arunderwood/milsblo/elec/src/parts/UNI_ROYAL_0603WAF1000T5E/R0603.STEP

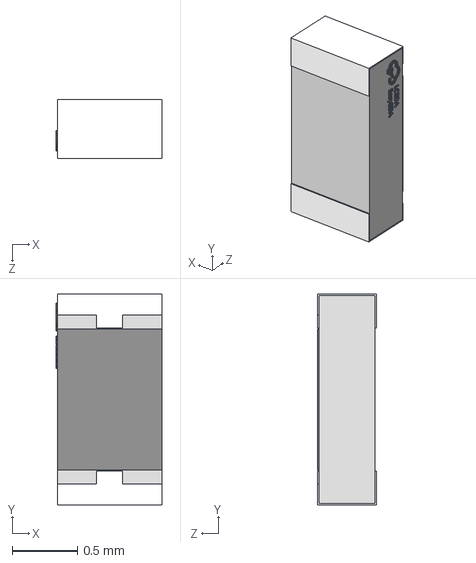
[picture p15: CAD file, 2026-02-18]
elec/src/parts/UNI_ROYAL_0603WAF1000T5E/R0603.STEP
0.81 x 1.62 x 0.45 mm
