arunderwood/milsblo/elec/src/parts/WCH_CH224K/ESSOP-10_L4.9-W3.9-P1.0-LS6.0-TL-EP.step

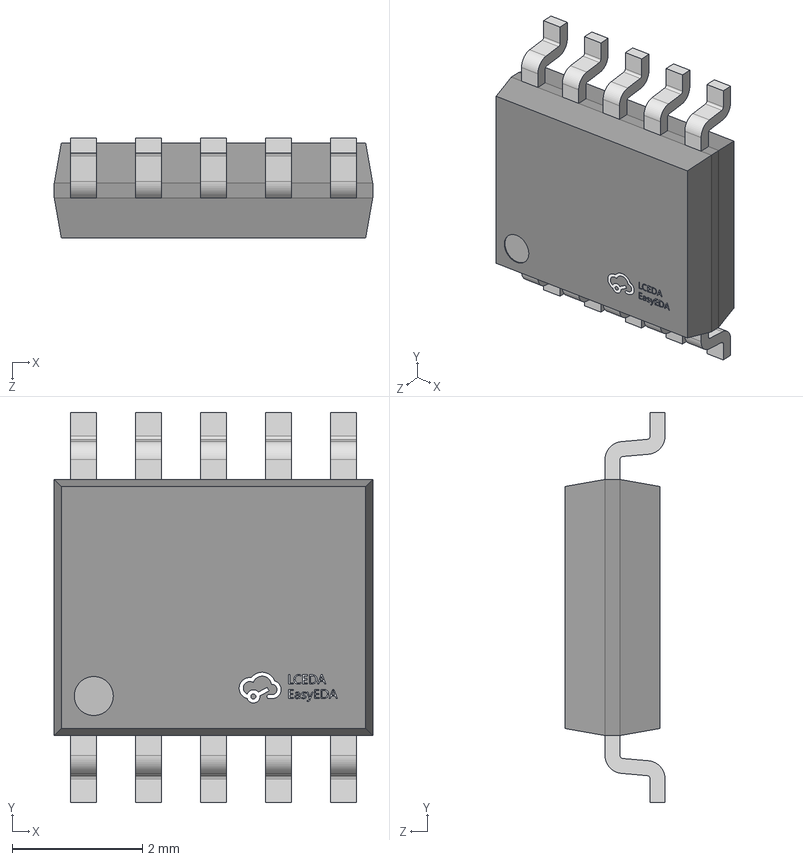
[picture p16: CAD file, 2026-02-18]
elec/src/parts/WCH_CH224K/ESSOP-10_L4.9-W3.9-P1.0-LS6.0-TL-EP.step
4.90 x 6.00 x 1.54 mm
