arunderwood/milsblo/elec/src/parts/YAGEO_CC0603KRX7R9BB104/C0603_L1.6-W0.8-H0.8.step

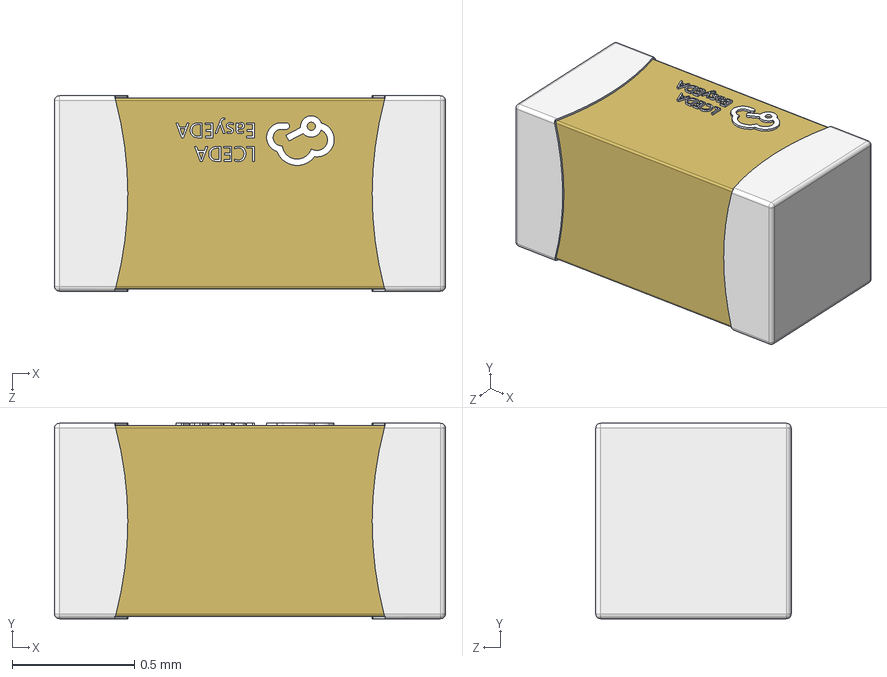
[picture p17: CAD file, 2026-02-18]
elec/src/parts/YAGEO_CC0603KRX7R9BB104/C0603_L1.6-W0.8-H0.8.step
1.60 x 0.8 x 0.8 mm
